HarrisonMauseth/pet-food-tracker/server/src/main/java/com/harrisonmauseth/petfoodtracker/security/WebSecurityConfig.java

package com.harrisonmauseth.petfoodtracker.security;

import org.springframework.beans.factory.annotation.Autowired;
import org.springframework.context.annotation.Bean;
import org.springframework.context.annotation.Configuration;
import org.springframework.security.authentication.AuthenticationManager;
import org.springframework.security.config.Customizer;
import org.springframework.security.config.annotation.authentication.configuration.AuthenticationConfiguration;
import org.springframework.security.config.annotation.web.builders.HttpSecurity;
import org.springframework.security.config.annotation.web.configuration.EnableWebSecurity;
import org.springframework.security.config.annotation.web.configurers.AbstractHttpConfigurer;
import org.springframework.security.config.http.SessionCreationPolicy;
import org.springframework.security.crypto.bcrypt.BCryptPasswordEncoder;
import org.springframework.security.crypto.password.PasswordEncoder;
import org.springframework.security.web.SecurityFilterChain;
import org.springframework.security.web.authentication.UsernamePasswordAuthenticationFilter;

/**
 * WebSecurityConfig provides the configuration for Spring Security.
 */
@Configuration
@EnableWebSecurity
public class WebSecurityConfig {

    private UserEntityDetailsService userDetailsService;
    private JwtAuthenticationEntryPoint authEntryPoint;
    private JwtFilter jwtFilter;

    @Autowired
    public WebSecurityConfig(UserEntityDetailsService userDetailsService,
                             JwtAuthenticationEntryPoint authEntryPoint, JwtFilter jwtFilter) {
        this.userDetailsService = userDetailsService;
        this.authEntryPoint = authEntryPoint;
        this.jwtFilter = jwtFilter;
    }

    @Bean
    public SecurityFilterChain filterChain(HttpSecurity httpSecurity) throws Exception {
        httpSecurity
                .csrf(AbstractHttpConfigurer::disable)
                .exceptionHandling((exceptionHandling) ->
                        exceptionHandling.accessDeniedPage("/errors/access-denied"))
                .authorizeHttpRequests(authorizationManagerRequestMatcherRegistry ->
                        authorizationManagerRequestMatcherRegistry
                                .requestMatchers("/register", "/login").permitAll()
                                .anyRequest().authenticated())
                .httpBasic(Customizer.withDefaults())
                .sessionManagement(httpSecuritySessionManagementConfigurer ->
                        httpSecuritySessionManagementConfigurer.sessionCreationPolicy(SessionCreationPolicy.STATELESS));

        httpSecurity.addFilterBefore(jwtFilter, UsernamePasswordAuthenticationFilter.class);

        return httpSecurity.build();
    }

    @Bean
    public AuthenticationManager authenticationManager(
            AuthenticationConfiguration authenticationConfiguration) throws Exception {
        return authenticationConfiguration.getAuthenticationManager();
    }

    @Bean
    PasswordEncoder passwordEncoder() {
        return new BCryptPasswordEncoder();
    }

}
